apanasara/Solar_roof_top/Media/Base pillar.jpeg

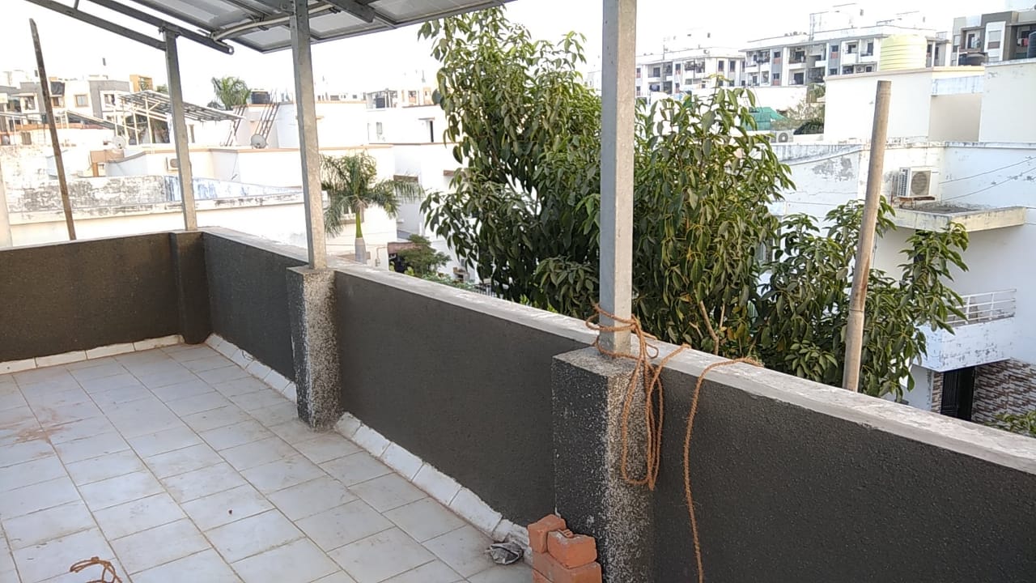
Media/Base pillar.jpeg
