apanasara/Solar_roof_top/Media/Lightning Arrestor.jpeg

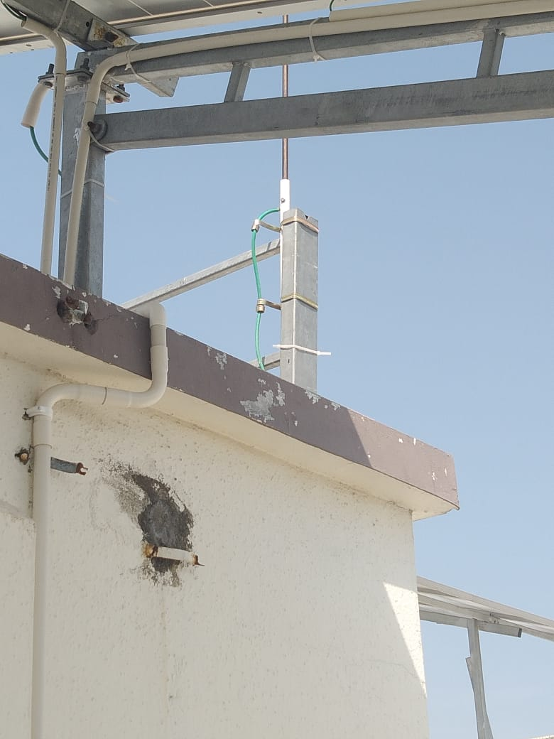
Media/Lightning Arrestor.jpeg
