apanasara/Solar_roof_top/Media/Structure Photos/2.jpeg

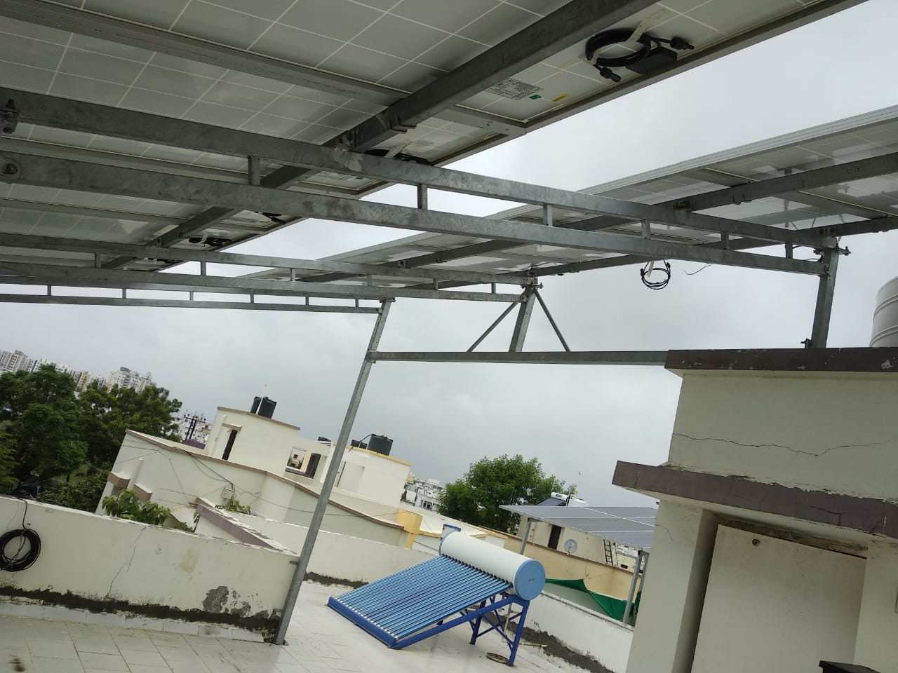
Media/Structure Photos/2.jpeg
