apanasara/Solar_roof_top/Media/Structure Photos/3.jpeg

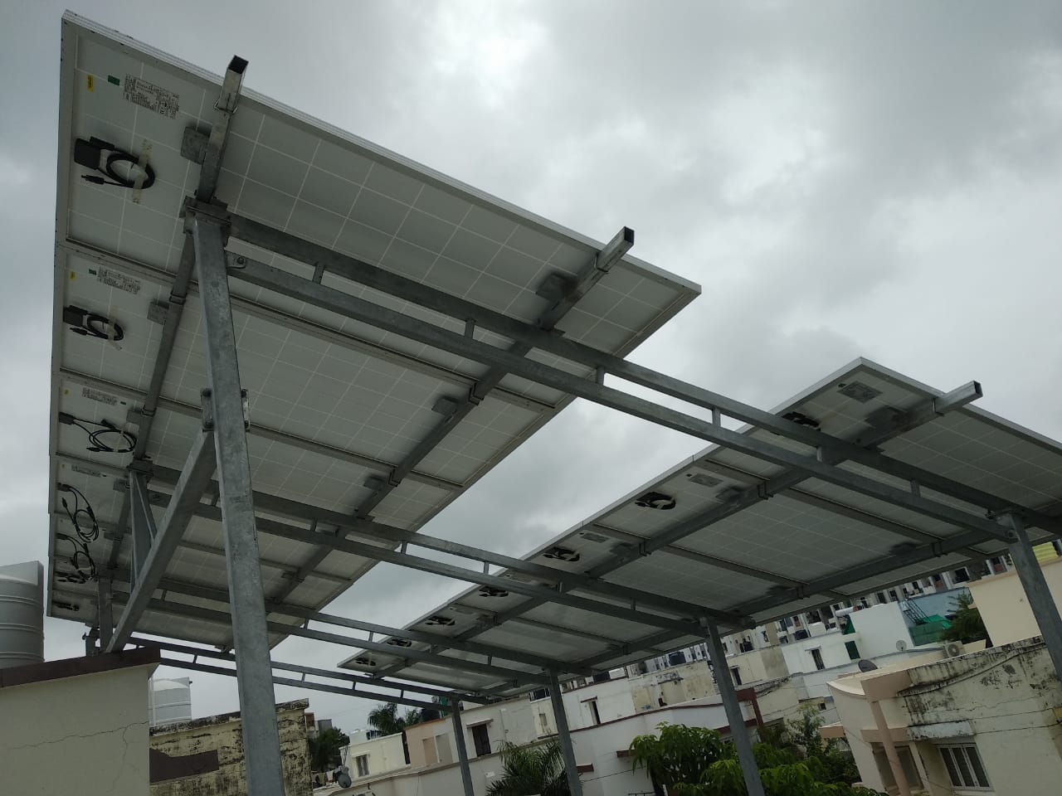
Media/Structure Photos/3.jpeg
