apanasara/Solar_roof_top/Media/Structure Photos/4.jpeg

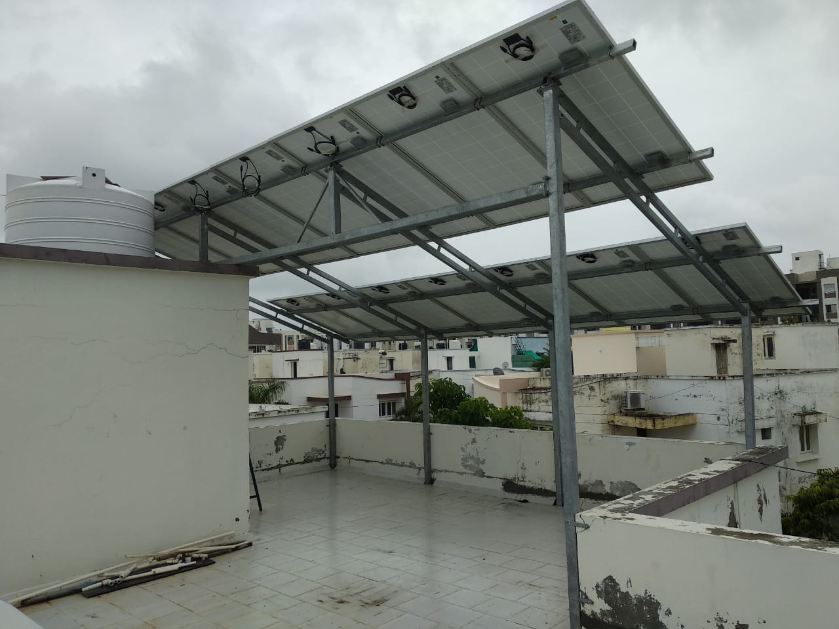
Media/Structure Photos/4.jpeg
