apanasara/Solar_roof_top/Media/Structure Photos/5.jpeg

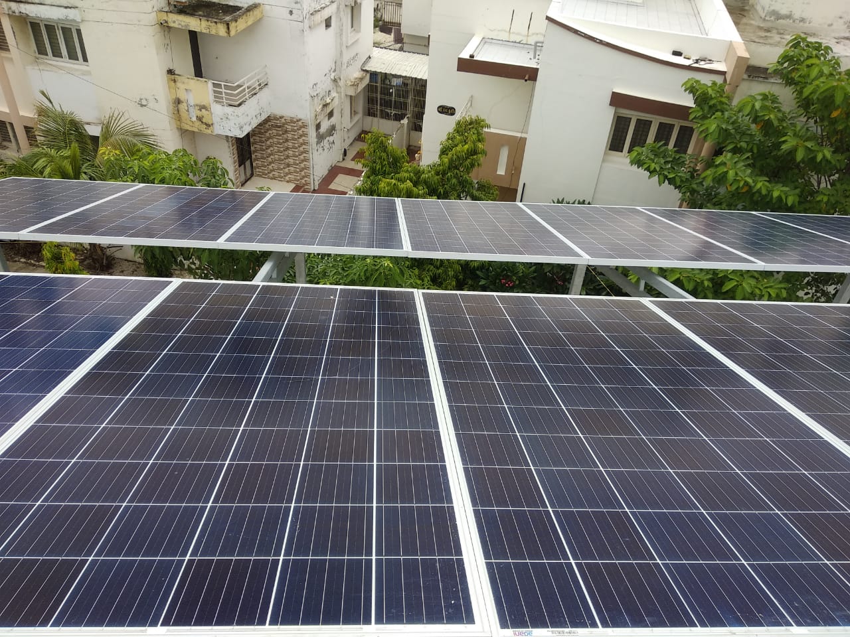
Media/Structure Photos/5.jpeg
