apanasara/Solar_roof_top/Media/Structure Photos/6.jpeg

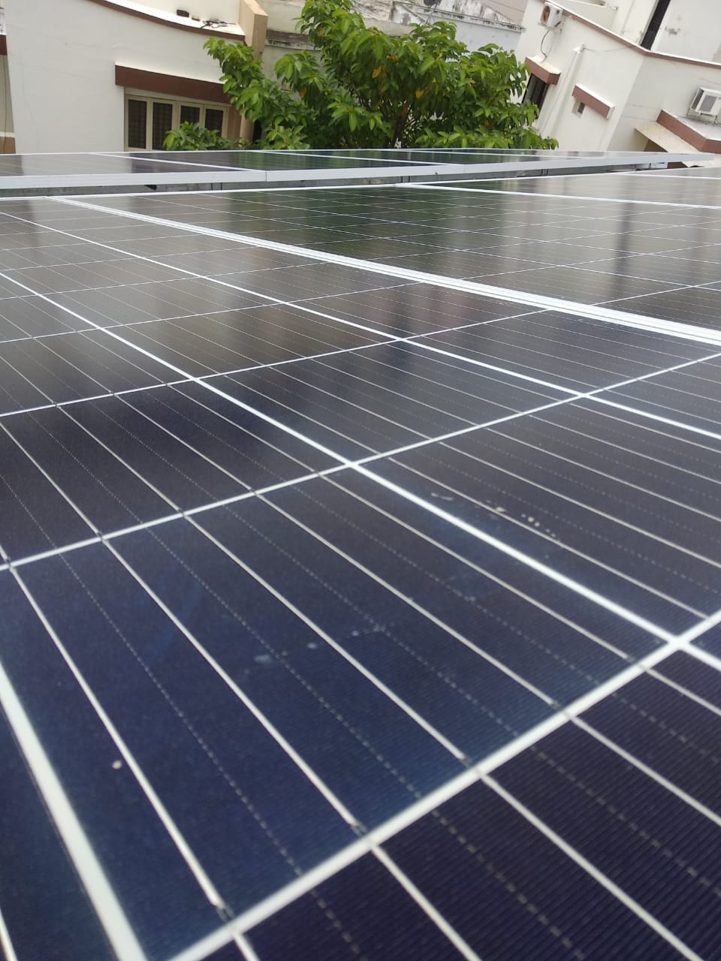
Media/Structure Photos/6.jpeg
