apanasara/Solar_roof_top/Media/Structure Photos/7.jpeg

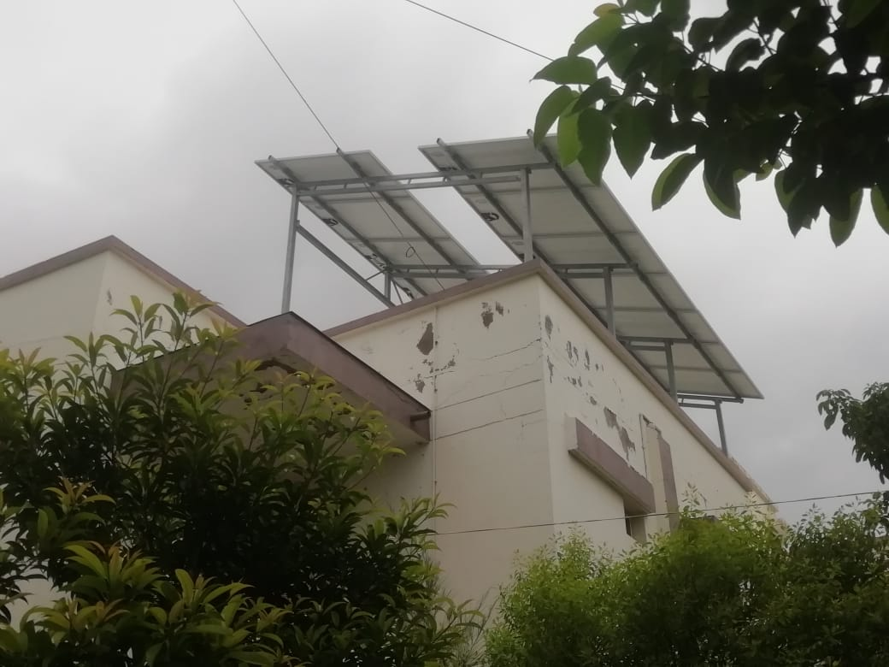
Media/Structure Photos/7.jpeg
