apanasara/Solar_roof_top/Media/Structure Photos/8.jpeg

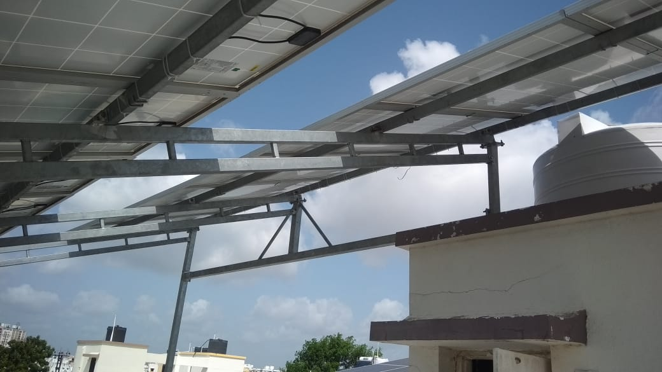
Media/Structure Photos/8.jpeg
