apanasara/Solar_roof_top/Media/Structure Photos/9.jpeg

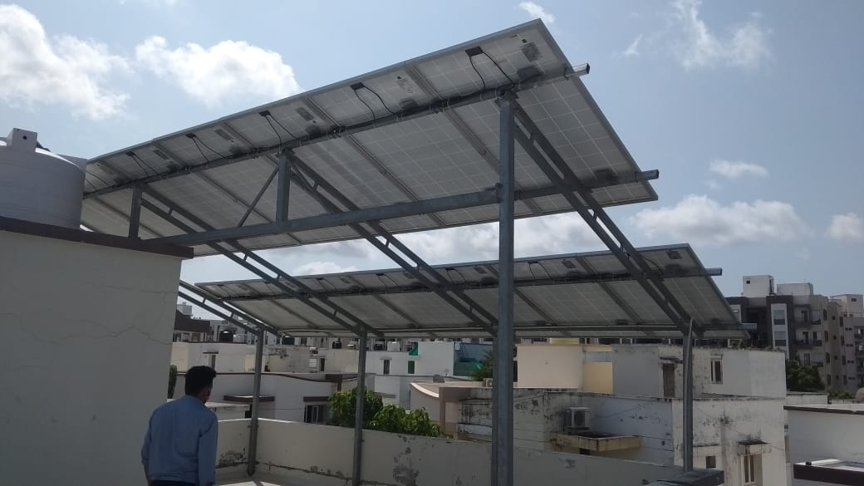
Media/Structure Photos/9.jpeg
