apanasara/Solar_roof_top/Media/Structure Photos/2020-09-21 at 17.30.12.jpeg

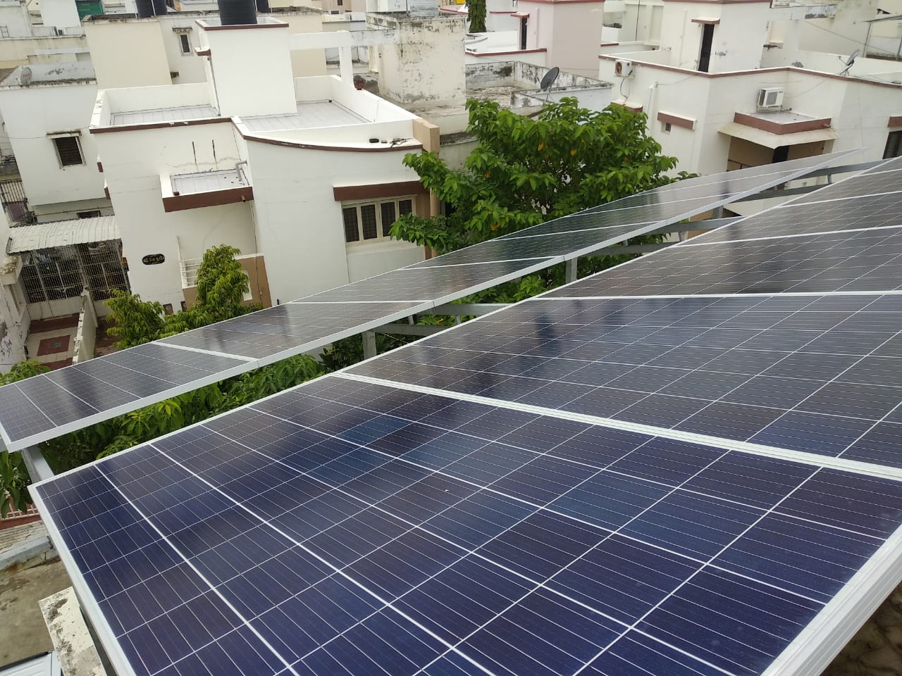
Media/Structure Photos/2020-09-21 at 17.30.12.jpeg
