apanasara/Solar_roof_top/Media/Structure Photos/Bare Structure 2020-07-19 at 20.40.20.jpeg

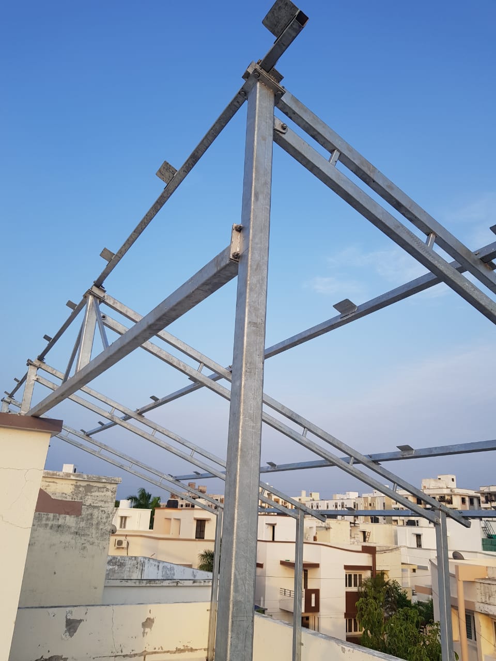
Media/Structure Photos/Bare Structure 2020-07-19 at 20.40.20.jpeg
