apanasara/Solar_roof_top/Structure Design Journey/02 Parallel Raft/Photos/Inspiration 2019-10-14 at 23.31.10.jpeg

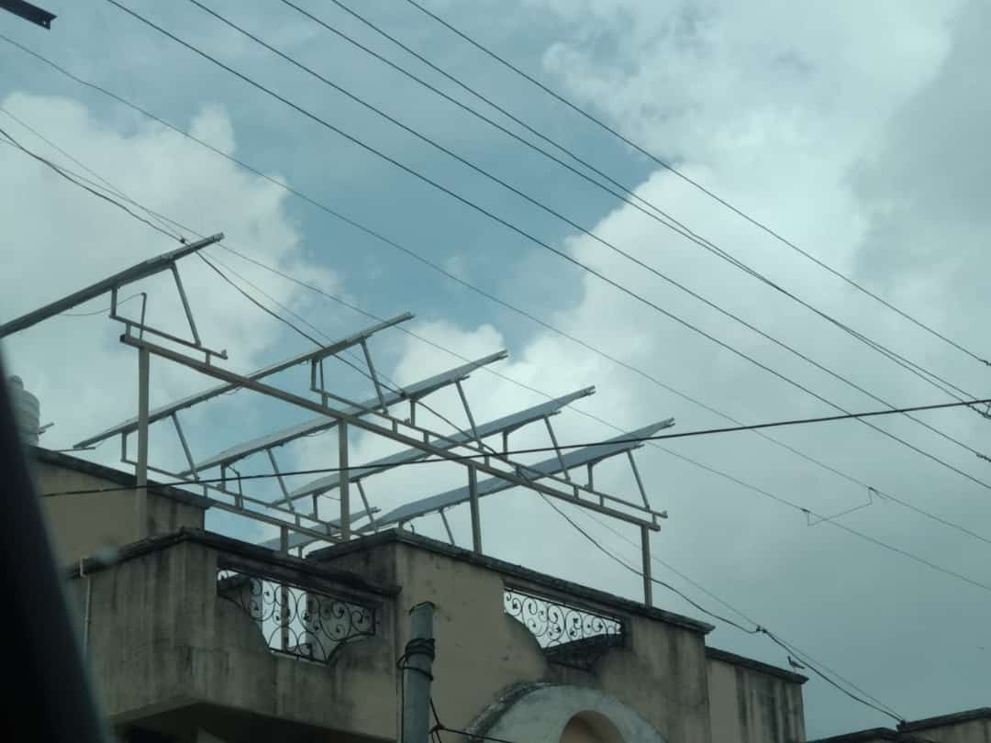
Structure Design Journey/02 Parallel Raft/Photos/Inspiration 2019-10-14 at 23.31.10.jpeg
