apanasara/Solar_roof_top/Structure Design Journey/03 Walk Way Single Raft (20deg South)/3D Photos/Ergonomics Study 2019-10-30 at 00.30.04.jpeg

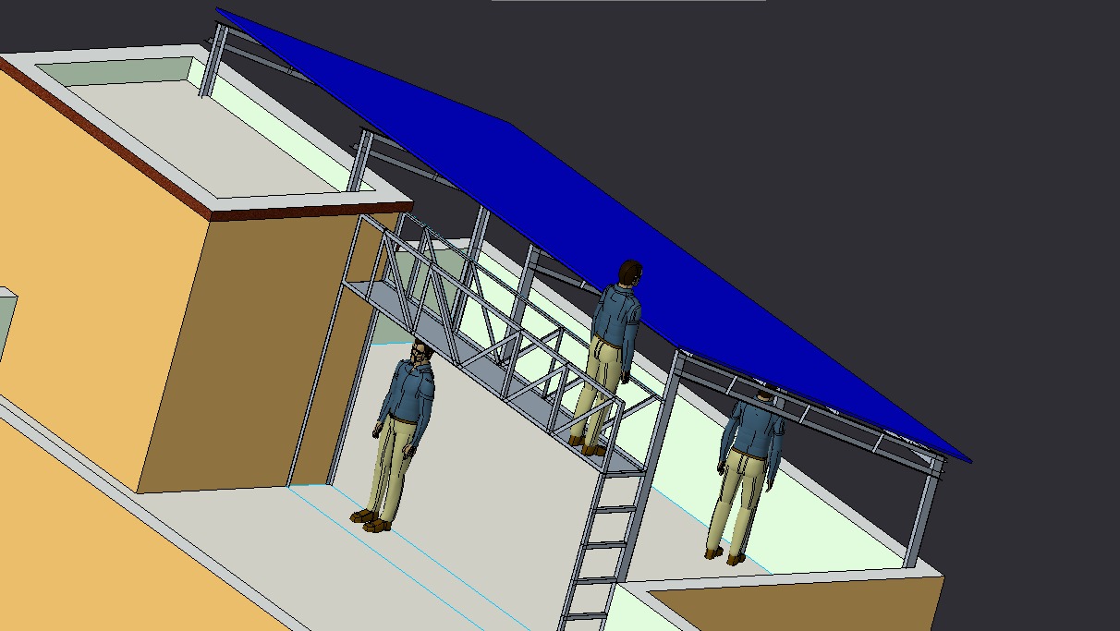
Structure Design Journey/03 Walk Way Single Raft (20deg South)/3D Photos/Ergonomics Study 2019-10-30 at 00.30.04.jpeg
