apanasara/Solar_roof_top/Structure Design Journey/03 Walk Way Single Raft (20deg South)/3D Photos/From West 2019-10-30 at 00.27.49.jpeg

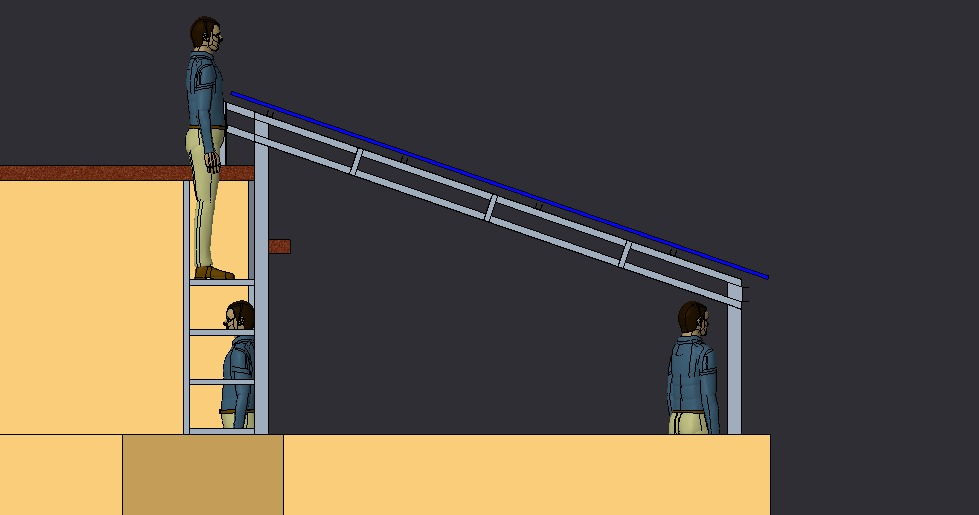
Structure Design Journey/03 Walk Way Single Raft (20deg South)/3D Photos/From West 2019-10-30 at 00.27.49.jpeg
