apanasara/Solar_roof_top/Structure Design Journey/03 Walk Way Single Raft (20deg South)/3D Photos/Staad Model 2019-11-28 at 09.08.49.jpeg

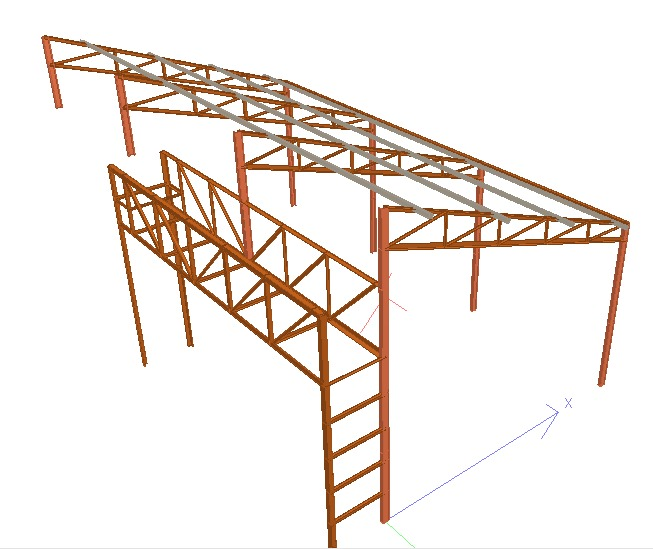
Structure Design Journey/03 Walk Way Single Raft (20deg South)/3D Photos/Staad Model 2019-11-28 at 09.08.49.jpeg
