apanasara/Solar_roof_top/Structure Design Journey/03 Walk Way Single Raft (20deg South)/3D Photos/Top 2019-10-30 at 00.34.52.jpeg

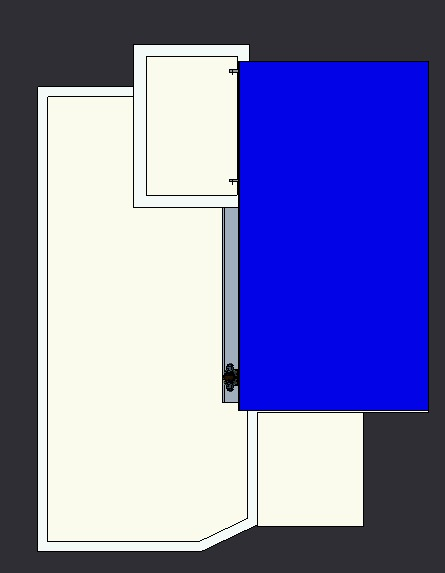
Structure Design Journey/03 Walk Way Single Raft (20deg South)/3D Photos/Top 2019-10-30 at 00.34.52.jpeg
