apanasara/Solar_roof_top/Structure Design Journey/03 Walk Way Single Raft (20deg South)/3D Photos/Walkway 2019-10-30 at 00.33.04.jpeg

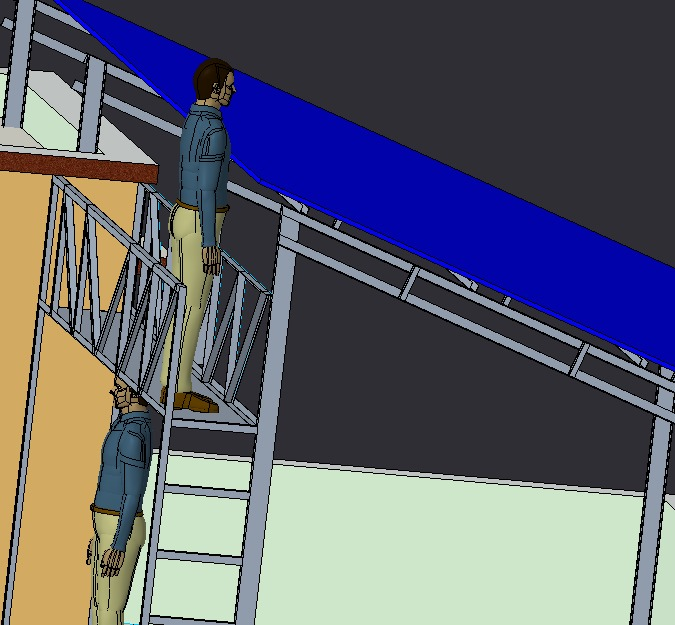
Structure Design Journey/03 Walk Way Single Raft (20deg South)/3D Photos/Walkway 2019-10-30 at 00.33.04.jpeg
