apanasara/Solar_roof_top/Structure Design Journey/03 Walk Way Single Raft (20deg South)/Shadow Analysis/Arrangement 2019-11-03 at 01.05.01.jpeg

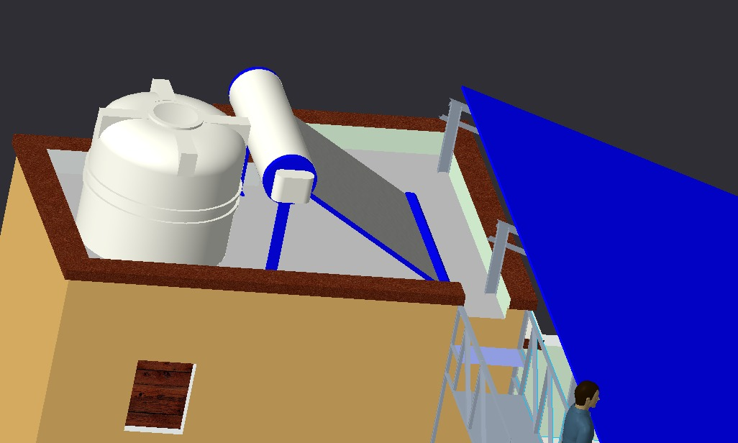
Structure Design Journey/03 Walk Way Single Raft (20deg South)/Shadow Analysis/Arrangement 2019-11-03 at 01.05.01.jpeg
