apanasara/Solar_roof_top/Material/Inverter/Inverter Selection 2019-10-15 at 10.34.30.jpeg

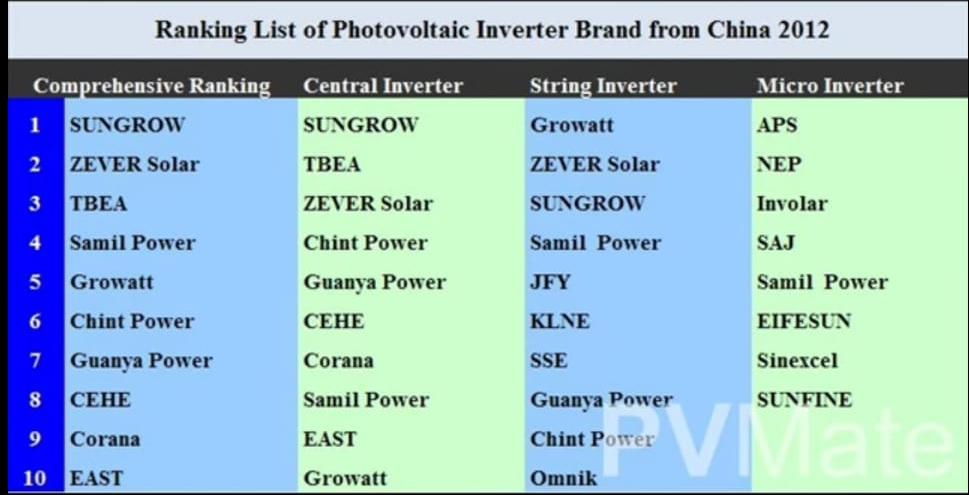
Material/Inverter/Inverter Selection 2019-10-15 at 10.34.30.jpeg
