apanasara/Solar_roof_top/Material/Inverter/Inverter.jpeg

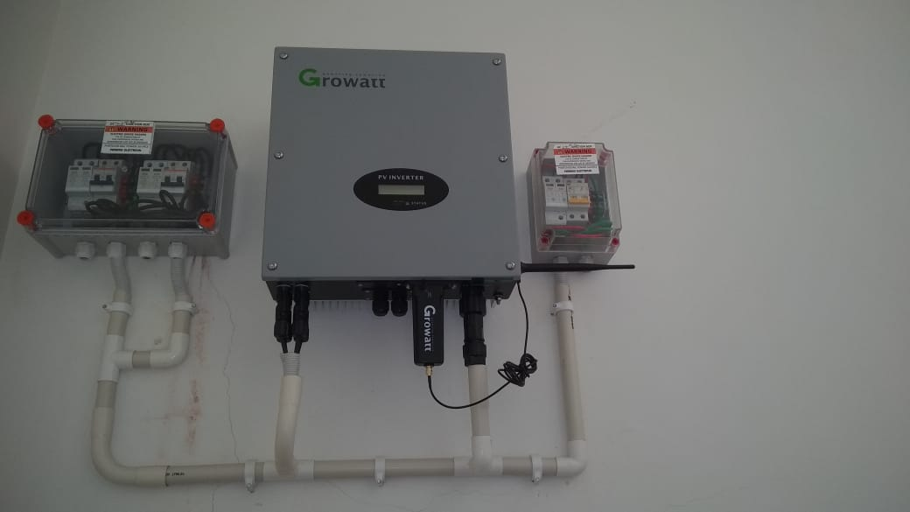
Material/Inverter/Inverter.jpeg
