apanasara/Solar_roof_top/Material/Inverter/Invoice of Inverter.jpeg

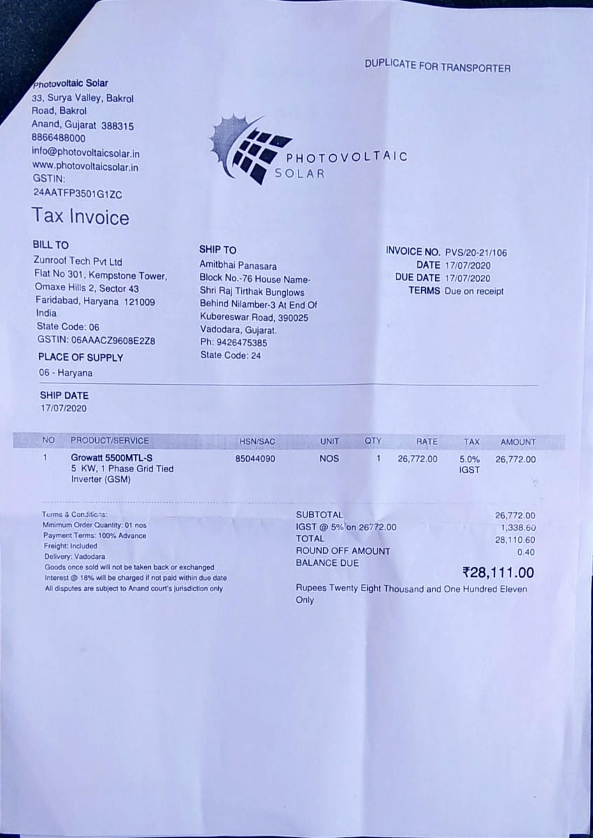
Material/Inverter/Invoice of Inverter.jpeg
