apanasara/Solar_roof_top/Material/PV Panel/PV Panel Bill 2020-07-29 at 22.12.03.jpeg

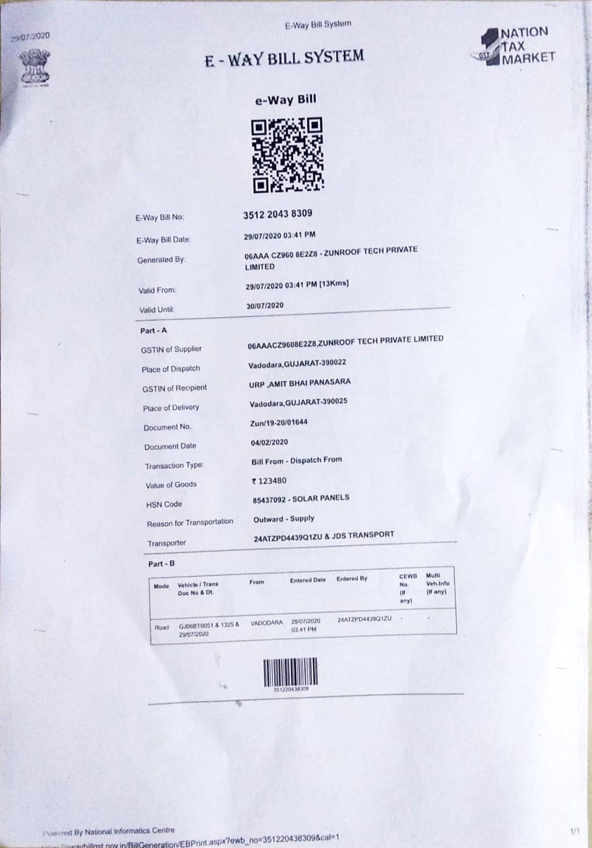
Material/PV Panel/PV Panel Bill 2020-07-29 at 22.12.03.jpeg
