apanasara/Solar_roof_top/Material/PV Panel/Panel make.jpeg

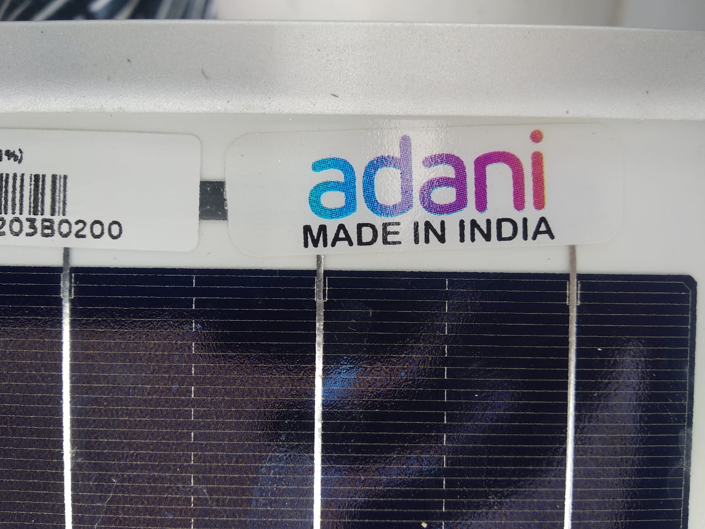
Material/PV Panel/Panel make.jpeg
