apanasara/Solar_roof_top/Media/Issue/Corrosion at Bi Metalic Junction/BiMetal Corrosion 2019-10-19 at 07.28.03.jpeg

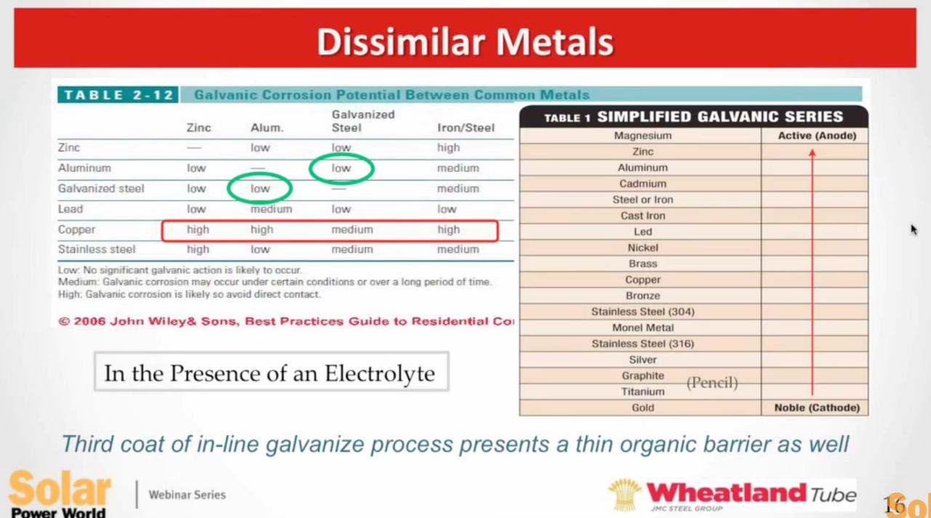
Media/Issue/Corrosion at Bi Metalic Junction/BiMetal Corrosion 2019-10-19 at 07.28.03.jpeg
