apanasara/Solar_roof_top/Media/Issue/Corrosion at Bi Metalic Junction/BiMetalic Stytem Consideration  2020-03-07 at 07.56.56.jpeg

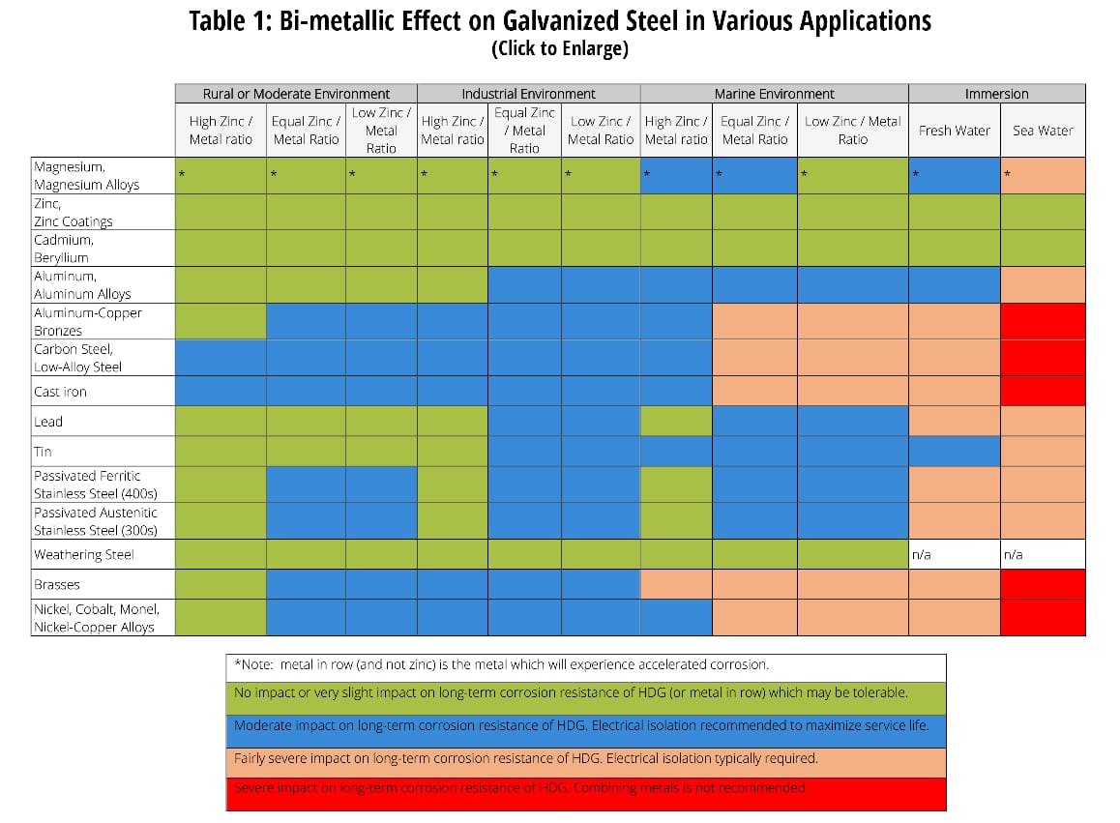
Media/Issue/Corrosion at Bi Metalic Junction/BiMetalic Stytem Consideration 2020-03-07 at 07.56.56.jpeg
