apanasara/Solar_roof_top/Media/Issue/Overhang Panel/Overhang Panel Deflection.jpeg

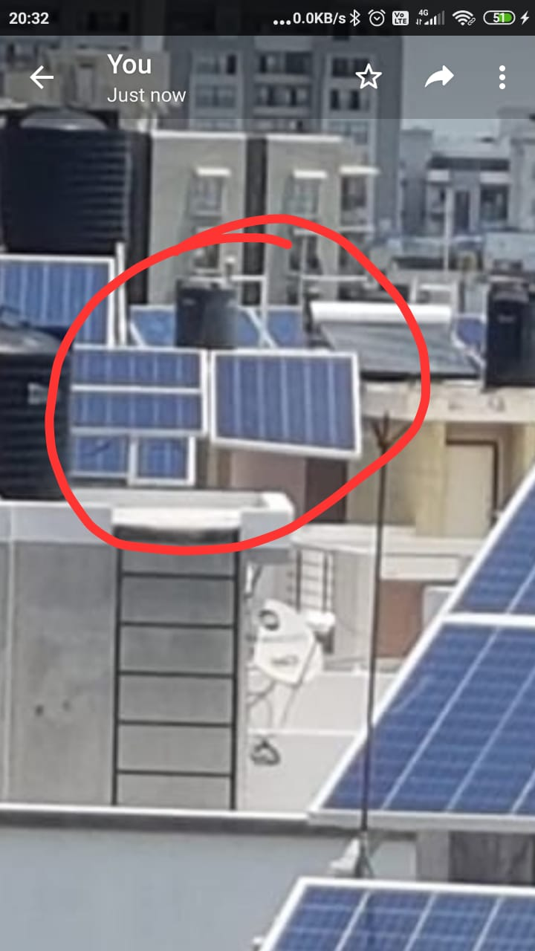
Media/Issue/Overhang Panel/Overhang Panel Deflection.jpeg
