apanasara/Solar_roof_top/Media/Issue/Rust On Open Joint/WhatsApp Image 2020-09-08 at 07.29.10.jpeg

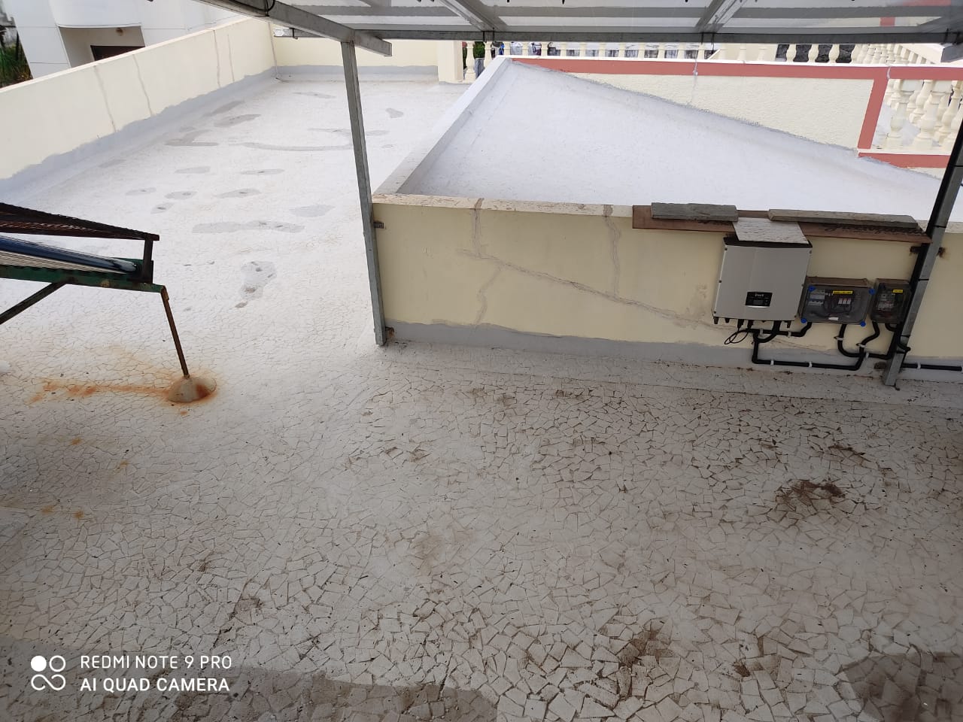
Media/Issue/Rust On Open Joint/WhatsApp Image 2020-09-08 at 07.29.10.jpeg
